Fescron/2ch-4-20mA-converter/hardware/1ch-4-20mA/Plots/1ch-4-20mA-F_Cu.pdf

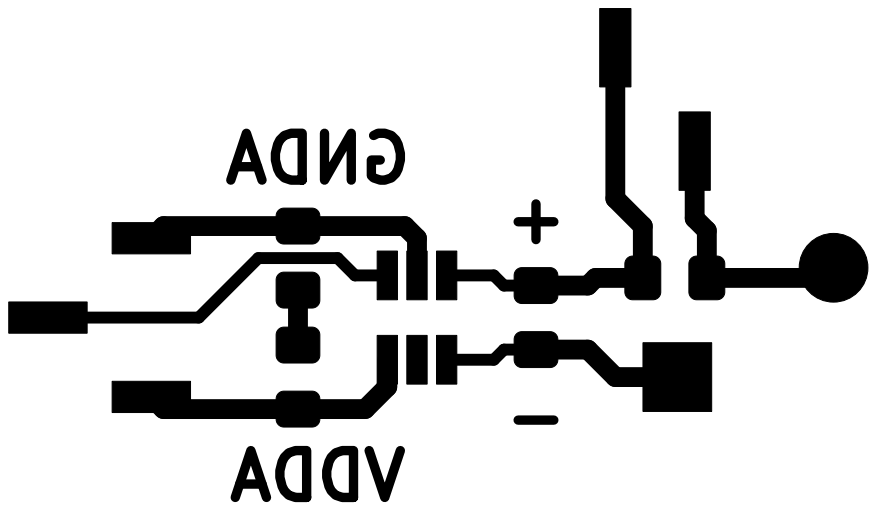
[picture p8: page 1]
